pepijndevos/accessibletuner/simulation2.asc

C1: cap; 1µ
C3: cap; 96n
C5: cap; 47n
C6: cap; 1µ
C7: cap; 47n
C8: cap; 0.1µ
C11: cap; 1µ
D1: schottky; BAT54
D2: schottky; BAT54
R1: res; 68k
R2: res; 68k
R3: res; 100k
R4: res; 100k
R6: res; 1Meg
R7: res; 1k
R9: res; 100k
R10: res; 1k
R12: res; 34k
R15: res; 10k
R18: res; 10k
U1: LT1413
U3: LT1413
U4: LT1413
U5: LT1413
V2: voltage; 5; Rser=0
V3: voltage; ""; AC 10m 0
Named nets: 0, 5V, sense, gain, input, 2.5V, filter
.ac dec 2000 0.1 100k
