pepijndevos/accessibletuner/simulation.asc

C1: cap; 1µ
C2: cap
C3: cap
C4: cap; 1µ
C5: cap
C6: cap; 1µ
C7: cap
C8: cap; 0.1µ
C9: cap; 1µ
C10: cap; 2.2µ
C11: cap
C12: cap; 470µ
D1: schottky; BAT54
D2: schottky; BAT54
L1: ind; 33µ
M1: nmos
M2: 
MN1: BS170
R1: res
R2: res
R3: res; 100k
R4: res; 100k
R5: res; 20k
R6: res; 10k
R7: res; 1k
R8: res; 10k
R9: res; 150k
R10: res; 1500
R11: res; 1k
R12: res
R13: res; 20Meg
R14: res; 10k
R15: res; 10k
R16: res
R17: res; 50
R18: res; 10k
U1: LT1413
U2: LT1413
U3: LT1413
U4: LT1413
U5: LT1413
V1: SINE(9 0.1 5000); Cpar=10
V2: SINE(5 0.1 5000); Rser=10
V3: SINE(0 0.01 80)
V5: PULSE(0 5 0.0001 0 0 0.0001 0.0002)
Named nets: 0, 9V, 5V, 2.5V, sense, reference, amp, gain, input, filter, pwm, heaphone
.tran 0.1
