pepijndevos/accessibletuner/agc_jfet.asc

C1: cap; 100µ
C2: cap; 10µ
D1: schottky; BAT54
J1: njf; BSR58/PLP
MN1: BS170
R1: res; 1k
R2: res; 10k
R3: res; 24k
R4: res; 50k
R5: res; 15k
R6: res; 3k
R7: res; 100k
R8: res; 1k
U2: opamp
V1: 2.5
V3: 2.5
V4: SINE(0 {VS} 82)
Named nets: VCC, VCC/2, 0, OUT, IN
.tran 0 0.2 0.1
.lib opamp.sub
.step param VS list 0.5m 1m 5m 10m
;dc V4 10m 1000m 10m
.lib phil_fet.lib
