pepijndevos/accessibletuner/piezo.asc

C1: cap; 10n
C2: cap; 1µ
C3: cap; 0.1µ
R1: res; 20Meg
R2: res; 10Meg
R3: res; 10Meg
R4: res; 100k
R5: res; 100k
U1: MCP6001
V1: 5; Rser=10 Cpar=1p
V2: SINE(0 0.1 50); Rser=10 Cpar=1p
V3: SINE(0 0.1 1)
Named nets: 0
.tran 0.1
.options gmin=1e-10
.options abstol=1e-10
.options reltol=0.003
.options cshunt=1e-13
